MortariMarco/EMOtto_ESP32_DIY/Collegamenti/Buzzer.png

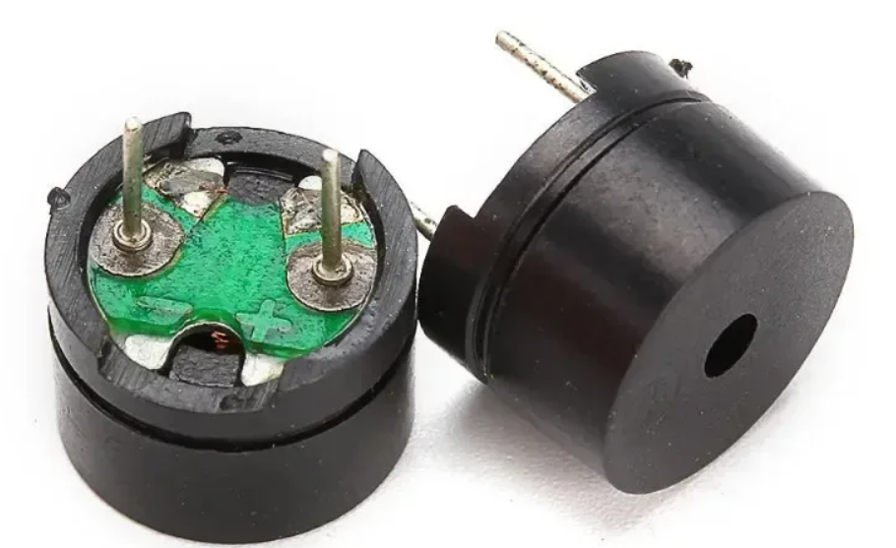
Collegamenti/Buzzer.png
