MortariMarco/EMOtto_ESP32_DIY/Collegamenti/Collegamenti.png

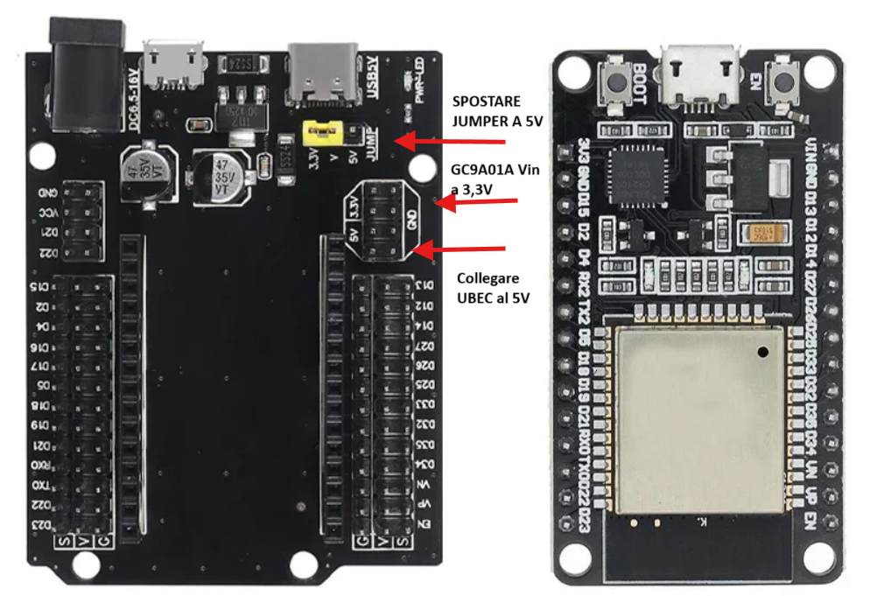
Collegamenti/Collegamenti.png
