MortariMarco/EMOtto_ESP32_DIY/Collegamenti/DFPlayerMini.png

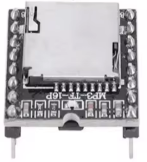
Collegamenti/DFPlayerMini.png
