MortariMarco/EMOtto_ESP32_DIY/Collegamenti/GC9A01A.png

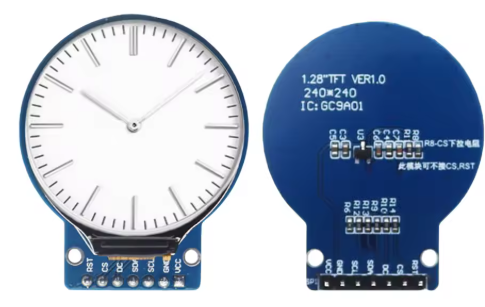
Collegamenti/GC9A01A.png
