MortariMarco/EMOtto_ESP32_DIY/Collegamenti/UBEC_5V_3A.png

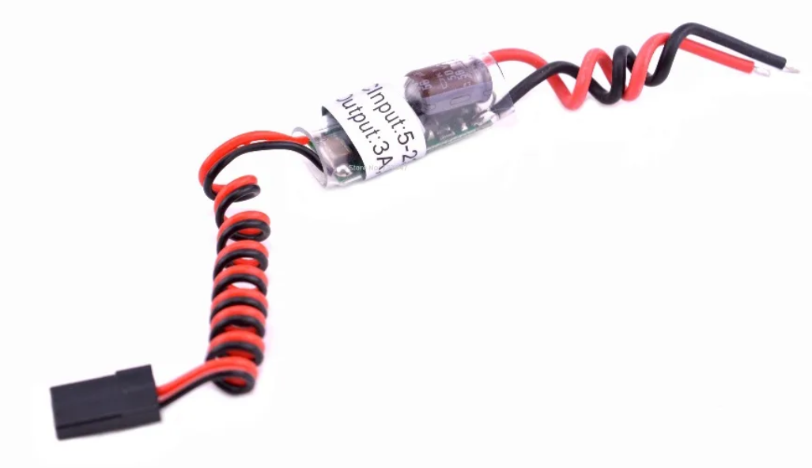
Collegamenti/UBEC_5V_3A.png
