MortariMarco/EMOtto_ESP32_DIY/Collegamenti/vl53l0x.png

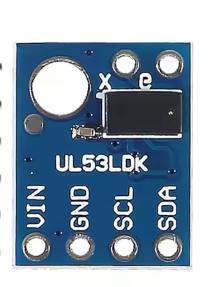
Collegamenti/vl53l0x.png
