MortariMarco/EMOtto_ESP32_DIY/Librerie/EMOttoDIYLib/src/dance4.cpp

#include "dance4.h"
#include "EMOtto.h"
#include "DFRobotDFPlayerMini.h"
//-- Happy
extern Otto Otto;
extern DFRobotDFPlayerMini myDFPlayer;

unsigned long music4Start = 0;
bool music4Started = false;
bool dance4Active = false;
bool music4Finished = false;
bool dance4Finished = false;
int danceIndex4 = 0;
unsigned long stepStart4 = 0;


typedef struct {
  void (*moveFunc)();
  unsigned long duration4;
} Dance4Move;

void move1_4() {
  Otto.moonwalker(1,950,30,1);
  Otto.moonwalker(1,950,30,-1);
  Otto.moonwalker(1,950,30,1); 
}//150
void move2_4() {
 Otto.home();
  Otto.moonwalker(1,1000,30,1);
  Otto.moonwalker(1,1000,30,-1);
  Otto.moonwalker(1,1000,30,1); 
 }//150
void move3_4() { 
   Otto.home();
  Otto.swing(3,1000,30);
 }//150
void move4_4() { 
  Otto.home();
  Otto.swing(3,1000,30);
  Otto.home();
 }
void move5_4() {   
Otto.ascendingTurn(8,870,30);
  Otto.home();
  Otto.jitter(8,900,30);
  Otto.moonwalker(1,950,30,1);
  Otto.moonwalker(1,950,30,-1);
  Otto.moonwalker(1,950,30,1); 
 }//150
void move6_4() {
  Otto.home();
  Otto.moonwalker(1,950,30,1);
  Otto.moonwalker(1,950,30,-1);
  Otto.moonwalker(1,950,30,1); 
}//-pausa 150
void move7_4() {
  Otto.home();
  Otto.swing(3,1000,30);
 }// pausa 150
void move8_4() {
  Otto.home();
  Otto.swing(3,1000,30);
  Otto.home();
  Otto.ascendingTurn(8,870,30);
  Otto.home();
  }
void move9_4() {
 Otto.jitter(8,900,30);
  Otto.moonwalker(1,950,30,1);
  Otto.moonwalker(1,950,30,-1);
  Otto.moonwalker(1,950,30,1); 
}// pausa 150
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

  unsigned long now = millis();

  if (danceIndex4 == -1 && now - music4Start > 1000 && dance4Active) {
    danceIndex4 = 0;
    stepStart4 = now;
    steps[danceIndex4].moveFunc();
    return;
  }

  if (danceIndex4 >= 0 && now - stepStart4 >= steps[danceIndex4].duration4) {
    danceIndex4++;

    // Se la danza è stata fermata, quando finisce il movimento corrente termina
    if (!dance4Active) {
      dance4Finished = true;
      Otto.home();
      Serial.println(">> Dance4 interrotta dopo movimento.");
      return;
    }

    if (danceIndex4 < NUM_STEPS4) {
      steps[danceIndex4].moveFunc();
      stepStart4 = now;
    } else {
      dance4Finished = true;
      dance4Active = false;
           danceIndex4 = -1; 
      Otto.home();
      Serial.println(">> Fine Dance4");
    }
  }
}




void stopDance4() {
  dance4Active = false;
  music4Finished = true;
  dance4Finished = true;
  myDFPlayer.stop();
  danceIndex4 = -1;  
  Otto.home();
  Serial.println(">> Dance4 stop richiesta.");
}



void toggleDance4() {
  if (dance4Active) {
    stopDance4();
  } else {
    startDance4();
  }
}

void updateMusic4Status() {
  if (!dance4Active) return;
  if (myDFPlayer.available()) {
    int type = myDFPlayer.readType();
    int value = myDFPlayer.read();
    if (type == DFPlayerPlayFinished && value == 37) {  // 37 è il brano dance4
      Serial.println(">> Musica dance4 finita");
      music4Finished = true;
      stopDance4();
    }
  }
}

bool isDance4Finished() {
  return dance4Finished;
}
